12zcab/Retro-Pad/3Dmodels/Caps/1x1.5 R3.stl

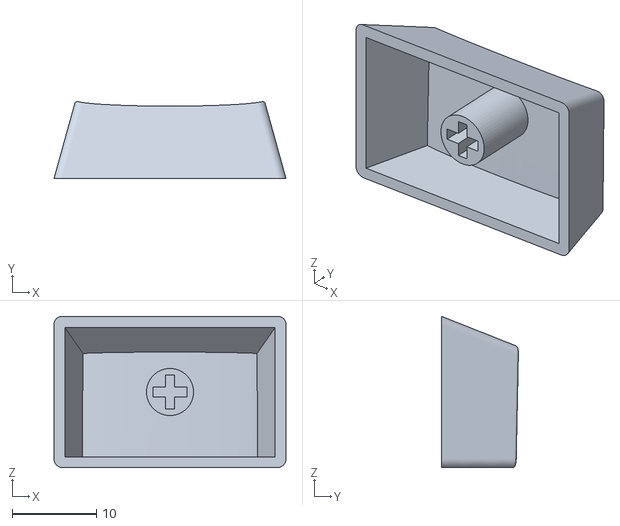
[picture p22: CAD file, 2026-06-10]
3Dmodels/Caps/1x1.5 R3.stl
27.6 x 9.14 x 18.0
